armysolo/BLV-AM8-MGN/Rail Relocation Mod/Pictures/Left Top.PNG

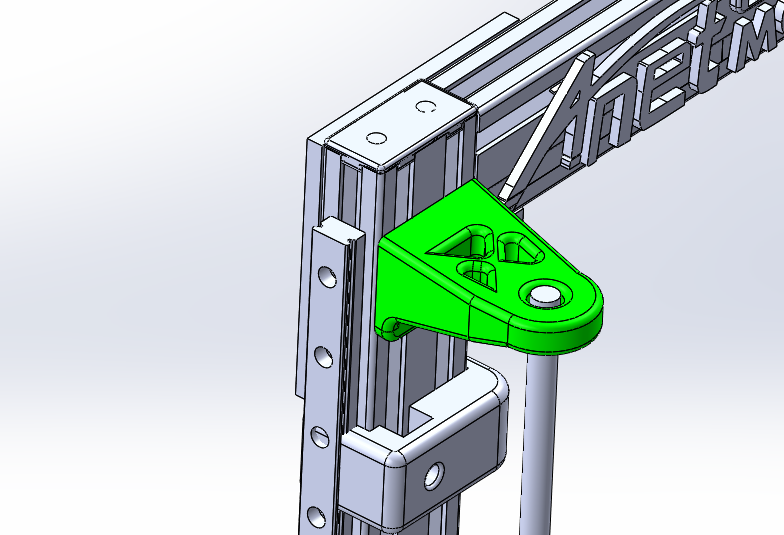
Rail Relocation Mod/Pictures/Left Top.PNG
