armysolo/BLV-AM8-MGN/Rail Relocation Mod/Pictures/Right Bottom.PNG

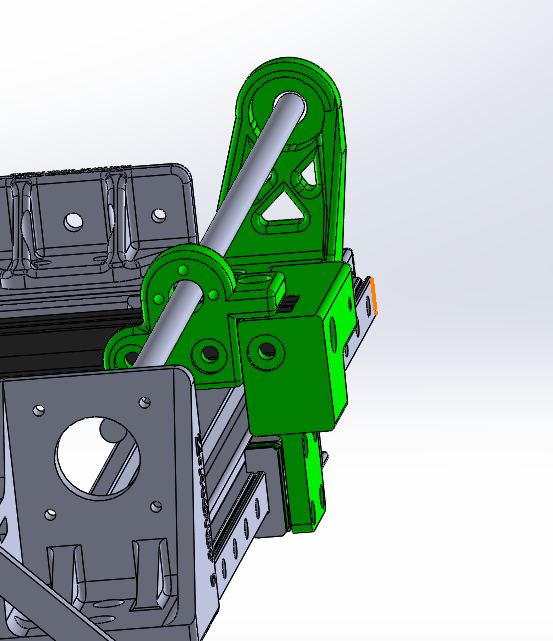
Rail Relocation Mod/Pictures/Right Bottom.PNG
