armysolo/BLV-AM8-MGN/Y Belt Tensioner Alternative/Capture.PNG

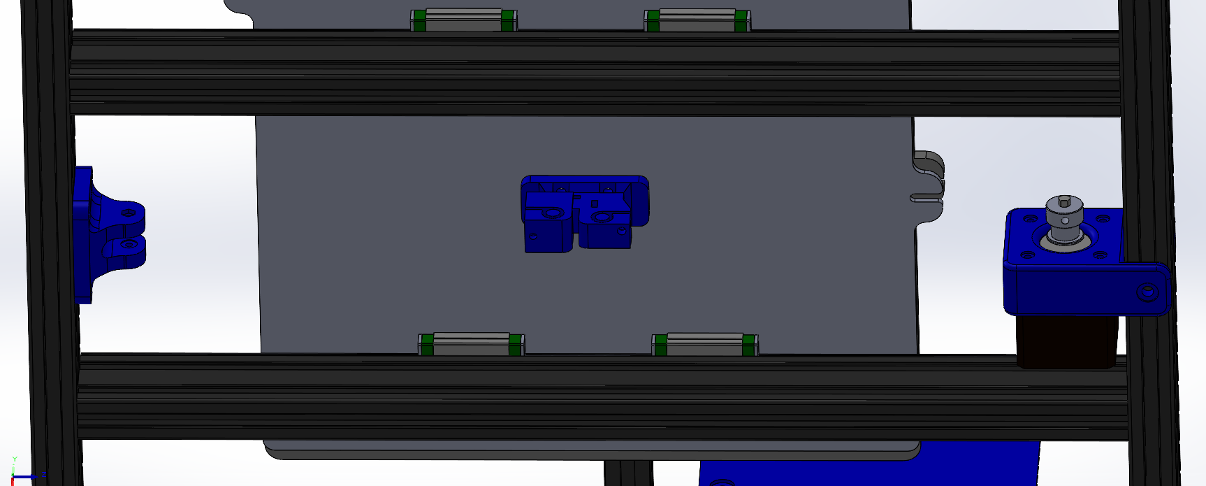
Y Belt Tensioner Alternative/Capture.PNG
