armysolo/BLV-AM8-MGN/Rail Relocation Mod/STL/BLV AM8 MGN Z Left Mount.STL

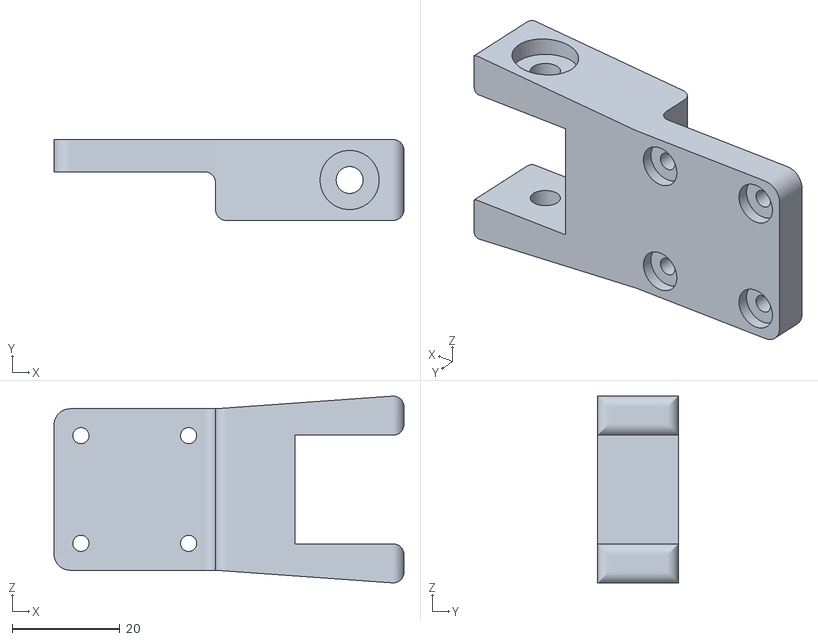
[picture p23: CAD file, 2021-03-24]
Rail Relocation Mod/STL/BLV AM8 MGN Z Left Mount.STL
65.0 x 15.0 x 34.7
