armysolo/BLV-AM8-MGN/BLV Cube X Carriage for AM8/STL/X Carriage - Top Cable Locker.STL

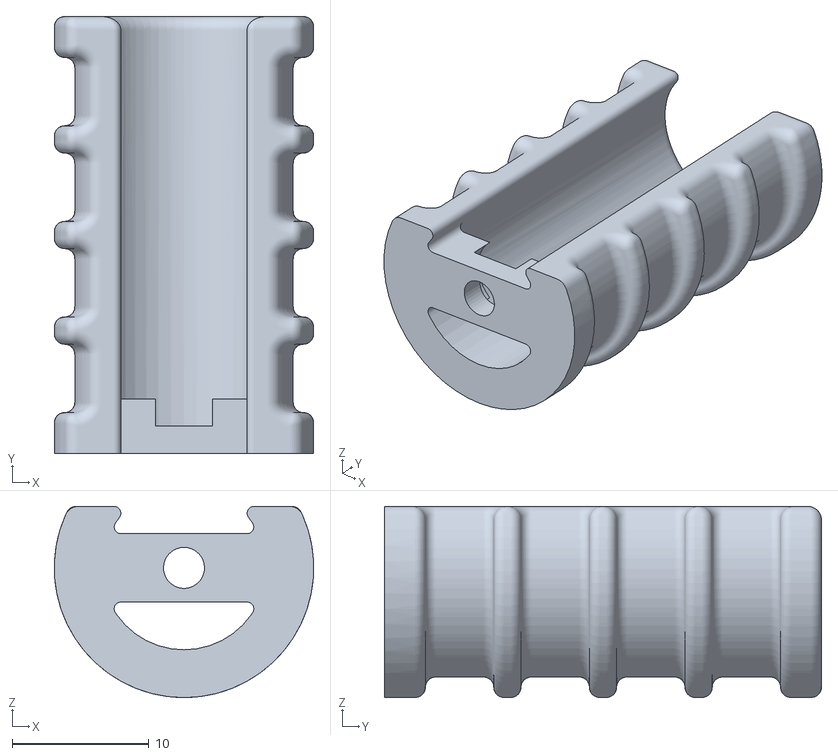
[picture p24: CAD file, 2021-03-24]
BLV Cube X Carriage for AM8/STL/X Carriage - Top Cable Locker.STL
19.0 x 32.0 x 14.0
