armysolo/BLV-AM8-MGN/BLV Cube X Carriage for AM8/STL/X Carriage - MGN Block.STL

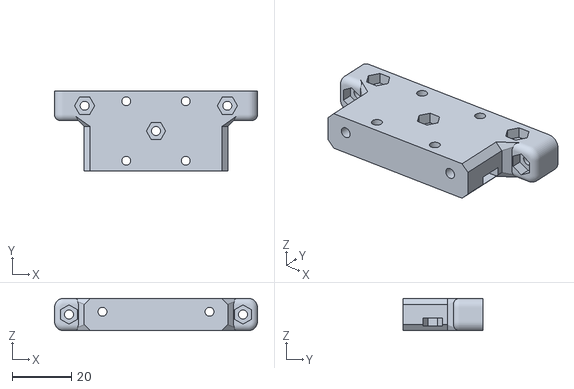
[picture p25: CAD file, 2021-03-24]
BLV Cube X Carriage for AM8/STL/X Carriage - MGN Block.STL
68.2 x 27.0 x 10.8
