armysolo/BLV-AM8-MGN/BLV Cube X Carriage for AM8/STL/X Carriage - Block Shield Twin Blower.STL

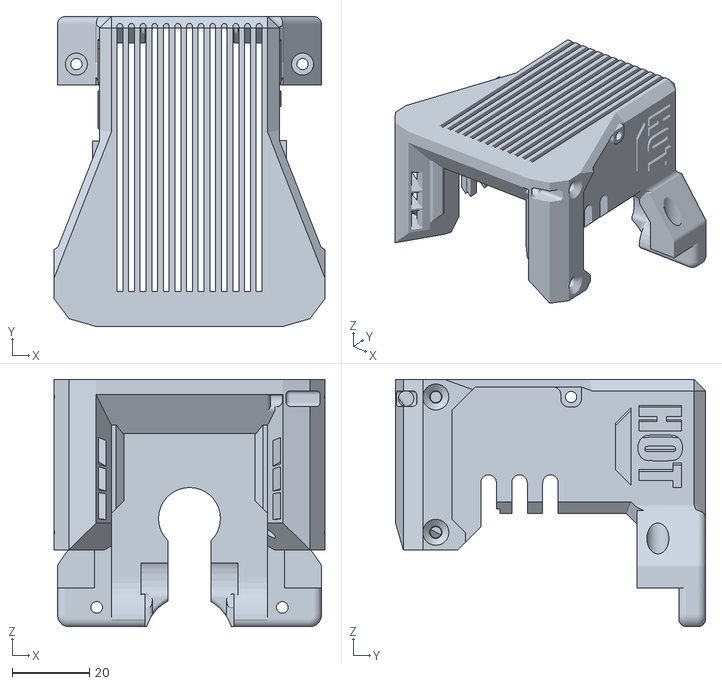
[picture p26: CAD file, 2021-03-24]
BLV Cube X Carriage for AM8/STL/X Carriage - Block Shield Twin Blower.STL
70.0 x 80.2 x 64.0
